fenix-squad/fenix/firmware/src/math.cpp

#ifndef __MATH__
#define __MATH__


#define PI 3.1415926535897932384626433832795
#include <cmath>

#include "./logs/log.cpp"
#include "./types/@package.cpp"
using namespace types;


inline f32 sins[360] = {
    0.0f,
    0.01745240643728351f,
    0.03489949670250097f,
    0.05233595624294383f,
    0.0697564737441253f,
    0.08715574274765817f,
    0.10452846326765346f,
    0.12186934340514748f,
    0.13917310096006544f,
    0.15643446504023087f,
    0.17364817766693033f,
    0.1908089953765448f,
    0.20791169081775931f,
    0.22495105434386498f,
    0.24192189559966773f,
    0.25881904510252074f,
    0.27563735581699916f,
    0.2923717047227367f,
    0.3090169943749474f,
    0.3255681544571567f,
    0.3420201433256687f,
    0.35836794954530027f,
    0.374606593415912f,
    0.3907311284892737f,
    0.40673664307580015f,
    0.42261826174069944f,
    0.4383711467890774f,
    0.45399049973954675f,
    0.4694715627858908f,
    0.48480962024633706f,
    0.49999999999999994f,
    0.5150380749100542f,
    0.5299192642332049f,
    0.544639035015027f,
    0.5591929034707468f,
    0.573576436351046f,
    0.5877852522924731f,
    0.6018150231520483f,
    0.6156614753256583f,
    0.6293203910498375f,
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
};

inline f32 coss[360] = {
    1.0f,
    0.9998476951563913f,
    0.9993908270190958f,
    0.9986295347545738f,
    0.9975640502598242f,
    0.9961946980917455f,
    0.9945218953682733f,
    0.992546151641322f,
    0.9902680687415704f,
    0.9876883405951378f,
    0.984807753012208f,
    0.981627183447664f,
    0.9781476007338057f,
    0.9743700647852352f,
    0.9702957262759965f,
    0.9659258262890683f,
    0.9612616959383189f,
    0.9563047559630355f,
    0.9510565162951535f,
    0.9455185755993168f,
    0.9396926207859084f,
    0.9335804264972017f,
    0.9271838545667874f,
    0.9205048534524404f,
    0.9135454576426009f,
    0.9063077870366499f,
    0.898794046299167f,
    0.8910065241883679f,
    0.882947592858927f,
    0.8746197071393957f,
    0.8660254037844387f,
    0.8571673007021123f,
    0.848048096156426f,
    0.838670567945424f,
    0.8290375725550417f,
    0.8191520442889918f,
    0.8090169943749475f,
    0.7986355100472928f,
    0.7880107536067219f,
    0.7771459614569709f,
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
};


namespace math {
    inline f32 sin(f32 a) {
        if (floor(a) == a) {
            return sins[u32(a)];
        } return std::sin(a / 180.0 * PI);
    }

    inline f32 cos(f32 a) {
        if (floor(a) == a) {
            return coss[u32(a)];
        } return std::cos(a / 180.0 * PI);
    }
};

#endif
