fenix-squad/fenix/firmware/src/deps.cpp

#ifndef __DEPS__
#define __DEPS__


#include <Arduino.h>

#include <SPI.h>
#include <USB.h>

#include <SPIFFS.h>
#include <FS.h>
using namespace fs;

#include <WiFi.h>
#include <ESPmDNS.h>
#include <ESPAsyncWebServer.h>

#include <driver/ledc.h>


#endif
